wrickert/badge/Documents/lid.png

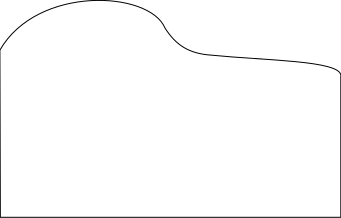
Documents/lid.png
