wrickert/badge/Firmware/rainbowPiano.py

import machine
import time
import utime
import neopixel
from notes import *
import random
import urandom

import esp32

pin13 = machine.Pin(13)
pin16 = machine.Pin(16, machine.Pin.IN, machine.Pin.PULL_UP)
speaker = machine.PWM(pin13)
speaker.duty(0)

current = 0
thresh = 500
colors = [(0,0,0),(0,0,0)]

t0 = machine.TouchPad(machine.Pin(4))
t1 = machine.TouchPad(machine.Pin(15))
t2 = machine.TouchPad(machine.Pin(12))
t3 = machine.TouchPad(machine.Pin(14))

t0.config(thresh)
t1.config(thresh)
t2.config(thresh)
t3.config(thresh)

np = neopixel.NeoPixel(machine.Pin(25), 10)
#np = neopixel.NeoPixel(machine.Pin(25), 10, bpp=4)

hx = machine.Pin(27, machine.Pin.PULL_UP)

esp32.wake_on_touch(True)


# This function controls adding colors to the neopixel strip
def stackColor(key):
    global colors

    if key == 1:
        colors.insert(0,(50,0,0))
    if key == 2:
        colors.insert(0,(0,50,0))
    if key == 3:
        colors.insert(0,(0,0,50))
    if key == 4:
        colors.insert(0,(40,40,0))

    print(colors)
    
    size = len(colors)
    if size > 10:
        size = 10
        colors.pop()

    for i in range(0, size): 
        np[i] = colors[i]

    np.write()

# Dimming to save battery life
def dimColors():
    global colors
    for i in range(10):
        if colors[i] == (50,0,0):
            np[i] = (2,0,0)
        elif colors[i] == (0,50,0):
            np[i] = (0,2,0)
        elif colors[i] == (0,0,50):
            np[i] = (0,0,2)
        elif colors[i] == (40,40,0):
            np[i] = (2,2,0)
        np.write()

# Program starts here
def keys():
    global thresh
    start = utime.time()
    dim = False
    dOff = False
    wait = False

    while True:
        try:
            if t0.read() < thresh and t1.read() < thresh and t2.read() < thresh and t3.read() < thresh:
                party()
            if t0.read() < thresh:
                time.sleep(0.02)
                if t0.read() < thresh:
                    setTone(1)
                start = utime.time()            
                if wait:
                    machine.freq(40000000)
                dim = False
                dOff = False
                wait = False
            elif t1.read() < thresh:
                time.sleep(0.02)
                if t1.read() < thresh:
                    setTone(2)
                start = utime.time()            
                if wait:
                    machine.freq(40000000)
                dim = False
                dOff = False
                wait = False
            elif t2.read() < thresh:
                time.sleep(0.02)
                if t2.read() < thresh:
                    setTone(3)
                start = utime.time()            
                if wait:
                    machine.freq(40000000)
                dim = False
                dOff = False
                wait = False
            elif t3.read() < thresh:
                time.sleep(0.02)
                if t3.read() < thresh:
                    setTone(4)
                start = utime.time()            
                if wait:
                    machine.freq(40000000)
                dim = False
                dOff = False
                wait = False
            else:
                setTone(0)

            if not pin16:
                flash()

            if ( utime.time() - start) > 30 and not dim and not wait:
                print("Dimming")    
                dim = True
                dimColors()
            if ( utime.time() - start) > 120 and not dOff and not wait:
                print("Display Off")
                dOff = True
                for i in range(10):
                    np[i] = (0,0,0)
                    time.sleep(0.02)
                    np.write()
                #start = utime.time()            
                wait = True
                machine.freq(20000000)

            # This bit of code takes the current consumption to ~4mA
            # but it causes a bit of delay to wake up from sleep
            # If that annoys you take it out and sleep will be ~14mA
            if wait:
                machine.sleep(1000)

        except ValueError:
            f = open('silent.txt', 'w')
            f.write('t')
            f.close()
            machine.reset()

def party():
    print("Big american party!")
    setTone(0)
    if t0.read() < thresh and t1.read() < thresh and t2.read() < thresh and t3.read() < thresh:
        while t0.read() < thresh:
            print("Move your fat fingers") 
    while True:
        for i in range(10):
            choice = urandom.randint(0,4)
            if choice == 0:
                np[i] = (255,0,0)
            if choice == 1:
                np[i] = (0,255,0)
            if choice == 2:
                np[i] = (0,0,255)
            if choice == 3:
                np[i] = (200,200,0)
            if choice == 4:
                np[i] = (0,0,0)
            #np[i] = (urandom.randint(0,255),urandom.randint(0,255),urandom.randint(0,255))
            np.write()
            time.sleep(0.05)
            if t0.read() < thresh and t1.read() < thresh and t2.read() < thresh and t3.read() < thresh:
                while t0.read() < thresh:
                    print("Move your fat fingers") 
                keys()


# Contols the piezo speaker
def setTone(key):
    global current
    if key == 0:
        speaker.duty(0)
        current = 0
    elif key == 1 and current != key:
        stackColor(1)
        print("1")
        speaker.duty(100)
        speaker.freq(G4)
        current = 1
    elif key == 2 and current != key:
        stackColor(2)
        print("2")
        speaker.duty(100)
        speaker.freq(B4)
        current = 2
    elif key == 3 and current != key:
        stackColor(3)
        print("3")
        speaker.duty(100)
        speaker.freq(CS5)
        current = 3
    elif key == 4 and current != key:
        stackColor(4)
        print("4")
        speaker.duty(100)
        speaker.freq(D5)
        current = 4

# Clears the display
def clear():
    for i in range(10):
        colors[i] = (0,0,0)
        np[i] = (0,0,0)
        np.write() 
        time.sleep(0.02)

# Highlights the Des Moines skyline silkscreen and welcome message
def inital():
    clear()
    print("Welcome to BSides Iowa 2019. Press Control+C to exit running program and enter REPL")
    np[2] = (0,0,50)
    np[3] = (0,0,50)
    np[4] = (0,0,50)
    np[5] = (0,0,50)
    np.write()

def play_note(freq: int, play_time: float = .2):
    """
    Plays a note of frequency `freq` for duration `play_time`, and lights up a random LED for fun
    :param freq: The frequency of the note to play, in hz
    :param play_time: The duration of the note, in seconds
    :return: Null
    """
    speaker.duty(100)
    speaker.freq(freq)
    stackColor(random.randint(1, 4))
    time.sleep(play_time)
    speaker.duty(0)
    
# This function checks the charing stats
def battery():
    if hx.value() == 0:
        print("Charged")
    else:
        print("Charging") 

# An attempt to make this eaiser to flash in bulk
def flash():
    print("Ready for flashing")
    sys.exit()
